kagouraki/YachtaWind_wifiToNmea183/Firmware/sloeber.ino.cpp

#ifdef __IN_ECLIPSE__
//This is a automatic generated file
//Please do not modify this file
//If you touch this file your change will be overwritten during the next build
//This file has been generated on 2022-05-24 00:31:44

#include "Arduino.h"
#include <WiFiManager.h>
#include <ESP_EEPROM.h>

void setup() ;
void checkButton() ;
String getParam(String name) ;
void switch_server() ;
void saveParamCallback() ;
void loop() ;


#include "WifiToNmea183.ino"

#endif
